armansinghh/pi-camera-proj/kicad/v1/v1.kicad_sch

## KiCad design kicad/v1/v1.kicad_sch (2026-08-25, an earlier design)

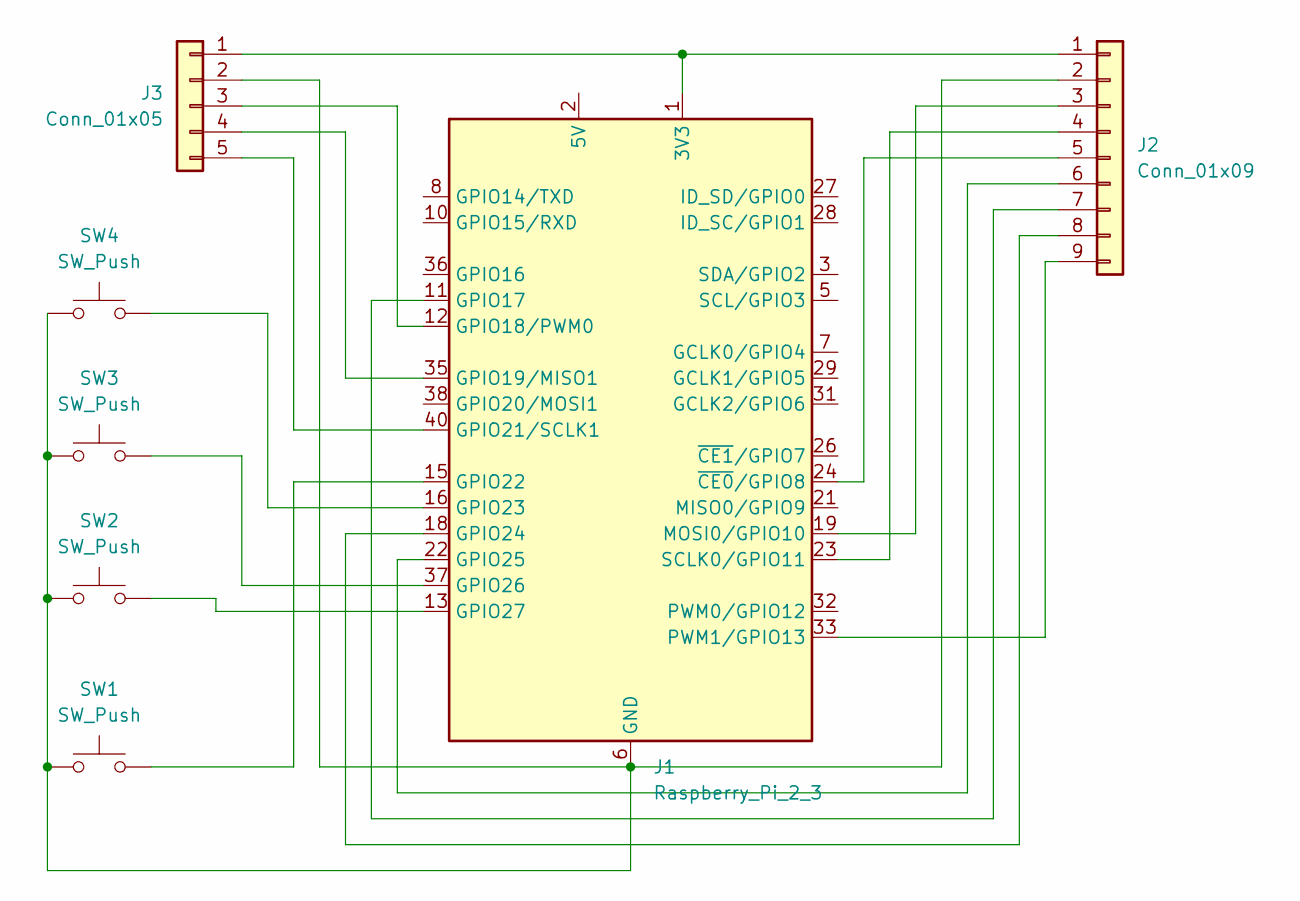
[picture p4: schematic v1.kicad_sch]

Parts:
J1: Raspberry_Pi_2_3
J2: Conn_01x09
J3: Conn_01x05
SW1, SW2, SW3, SW4: SW_Push

Connections:
unnamed: J1.1 (3V3), J1.17 (3V3), J2.1, J3.1
unnamed: J1.2 (5V), J1.4 (5V)
unnamed: J1.11 (GPIO17), J2.7
unnamed: J1.12 (GPIO18/PWM0), J3.3
unnamed: J1.13 (GPIO27), SW2.2
unnamed: J1.6 (GND), J1.9 (GND), J1.14 (GND), J1.20 (GND), J1.25 (GND), J1.30 (GND), J1.34 (GND), J1.39 (GND), J2.2, J3.2, SW1.1, SW2.1, SW3.1, SW4.1
unnamed: J1.15 (GPIO22), SW1.2
unnamed: J1.16 (GPIO23), SW4.2
unnamed: J1.18 (GPIO24), J2.8
unnamed: J1.19 (MOSI0/GPIO10), J2.3
unnamed: J1.22 (GPIO25), J2.6
unnamed: J1.23 (SCLK0/GPIO11), J2.4
unnamed: J1.24 (~CE0/GPIO8), J2.5
unnamed: J1.33 (PWM1/GPIO13), J2.9
unnamed: J1.35 (GPIO19/MISO1), J3.4
unnamed: J1.37 (GPIO26), SW3.2
unnamed: J1.40 (GPIO21/SCLK1), J3.5
