armansinghh/pi-camera-proj/kicad/v2/v2.kicad_sch

## KiCad design kicad/v2/v2.kicad_sch (2026-08-28)

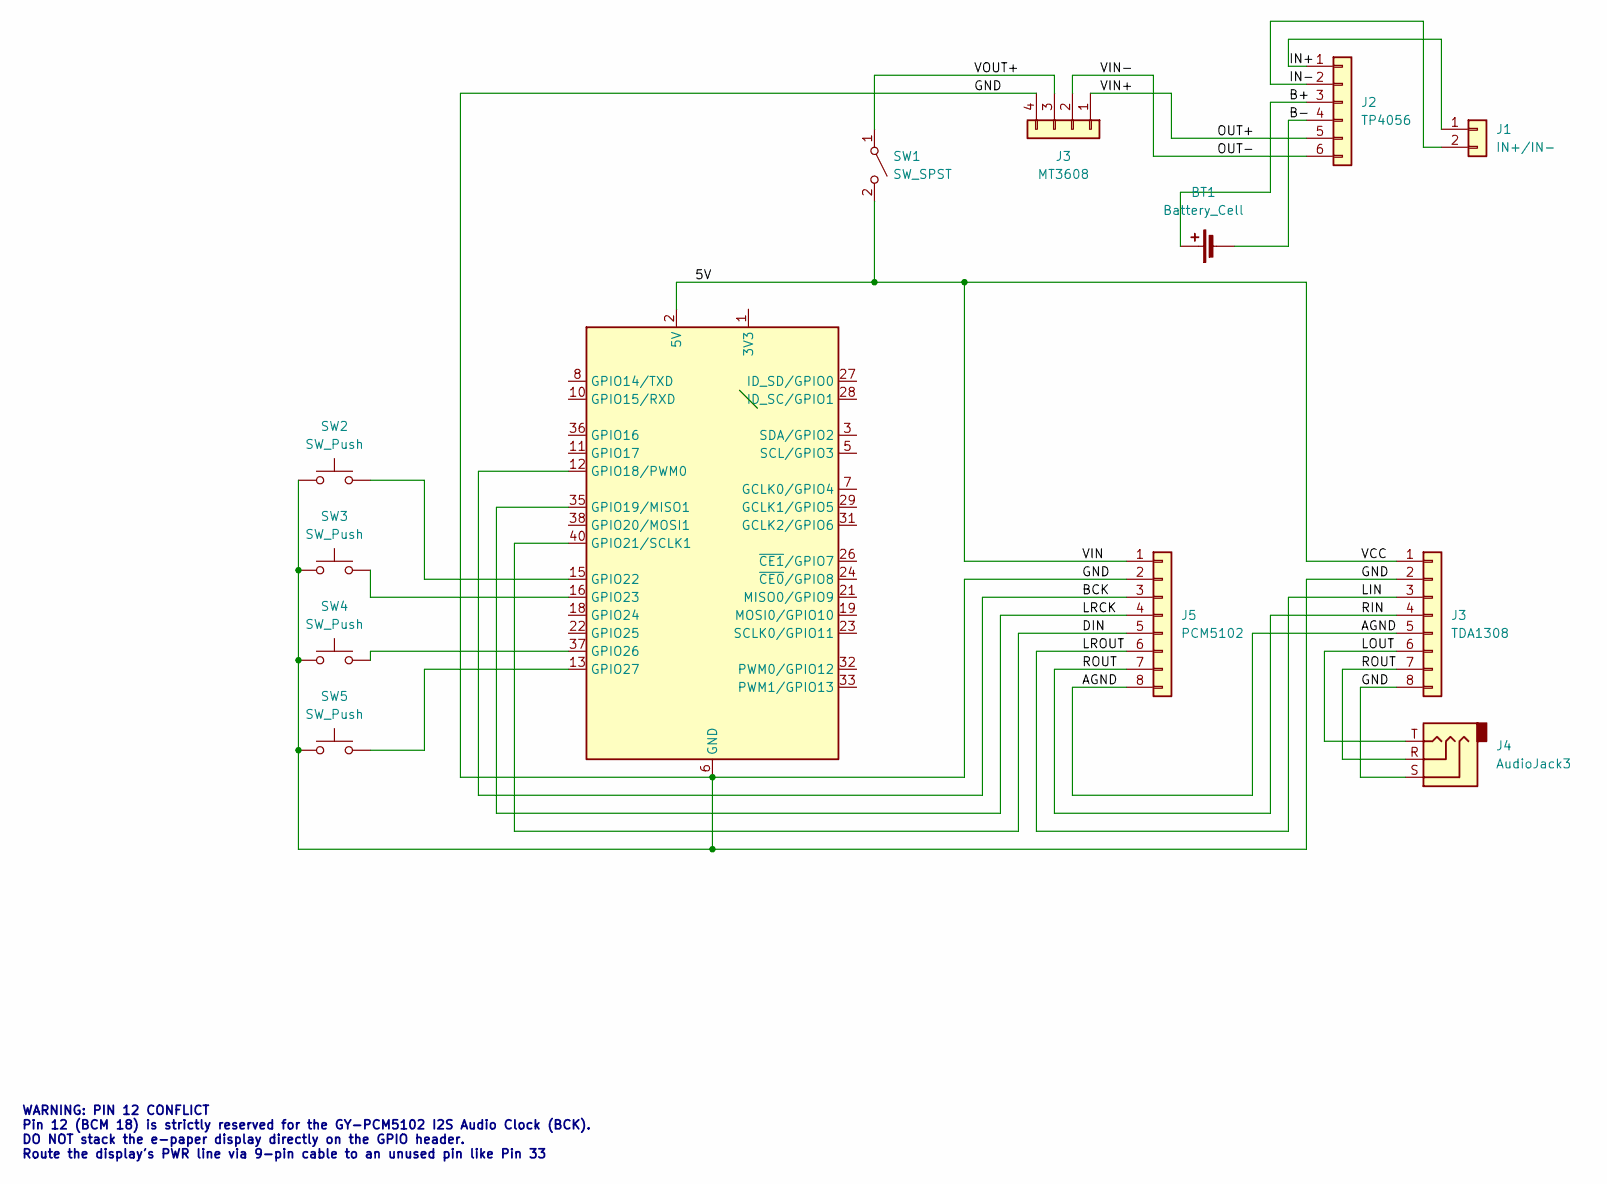
[picture p5: schematic v2.kicad_sch]

Parts:
BT1: Battery_Cell
J1: IN+/IN-
J2: TP4056
J3: MT3608
J4: AudioJack3
J5: PCM5102
SW1: SW_SPST
SW2, SW3, SW4, SW5: SW_Push

Connections:
5V: J2.2 (5V), J2.4 (5V), J3.1, J5.1, SW1.2 (B)
AGND: J3.5, J5.8
B+: BT1.1 (+), J2.3 (SDA/GPIO2)
B-: BT1.2 (-), J2.4 (5V)
BCK: J2.12 (GPIO18/PWM0), J5.3
DIN: J2.40 (GPIO21/SCLK1), J5.5
GND: J2.6 (GND), J2.9 (GND), J2.14 (GND), J2.20 (GND), J2.25 (GND), J2.30 (GND), J2.34 (GND), J2.39 (GND), J3.2, J3.4, J3.8, J4.S, J5.2, SW2.1, SW3.1, SW4.1, SW5.1
IN+: J1.1, J2.1 (3V3)
IN-: J1.2, J2.2 (5V)
LIN: J3.3, J5.6
LOUT: J3.6, J4.T
LRCK: J2.35 (GPIO19/MISO1), J5.4
unnamed: J2.1 (3V3), J2.17 (3V3)
unnamed: J2.13 (GPIO27), SW5.2
unnamed: J2.15 (GPIO22), SW2.2
unnamed: J2.16 (GPIO23), SW3.2
unnamed: J2.37 (GPIO26), SW4.2
OUT+: J2.5 (SCL/GPIO3), J3.1
OUT-: J2.6 (GND), J3.2
RIN: J3.4, J3.7, J4.R, J5.7
VOUT+: J3.3, SW1.1 (A)

Notes on the sheet:
WARNING: PIN 12 CONFLICT Pin 12 (BCM 18) is strictly reserved for the GY-PCM5102 I2S Audio Clock (BCK). DO NOT stack the e-paper display directly on the GPIO header. Route the display's PWR line via 9-pin cable to an unused pin like Pin 33
